Maheemal/Spacemouse-Macro-Keys/Source Files/PCB/Spacemouse-Macro-Keys.kicad_sch

## KiCad design Source Files/PCB/Spacemouse-Macro-Keys.kicad_sch (2022-12-31)

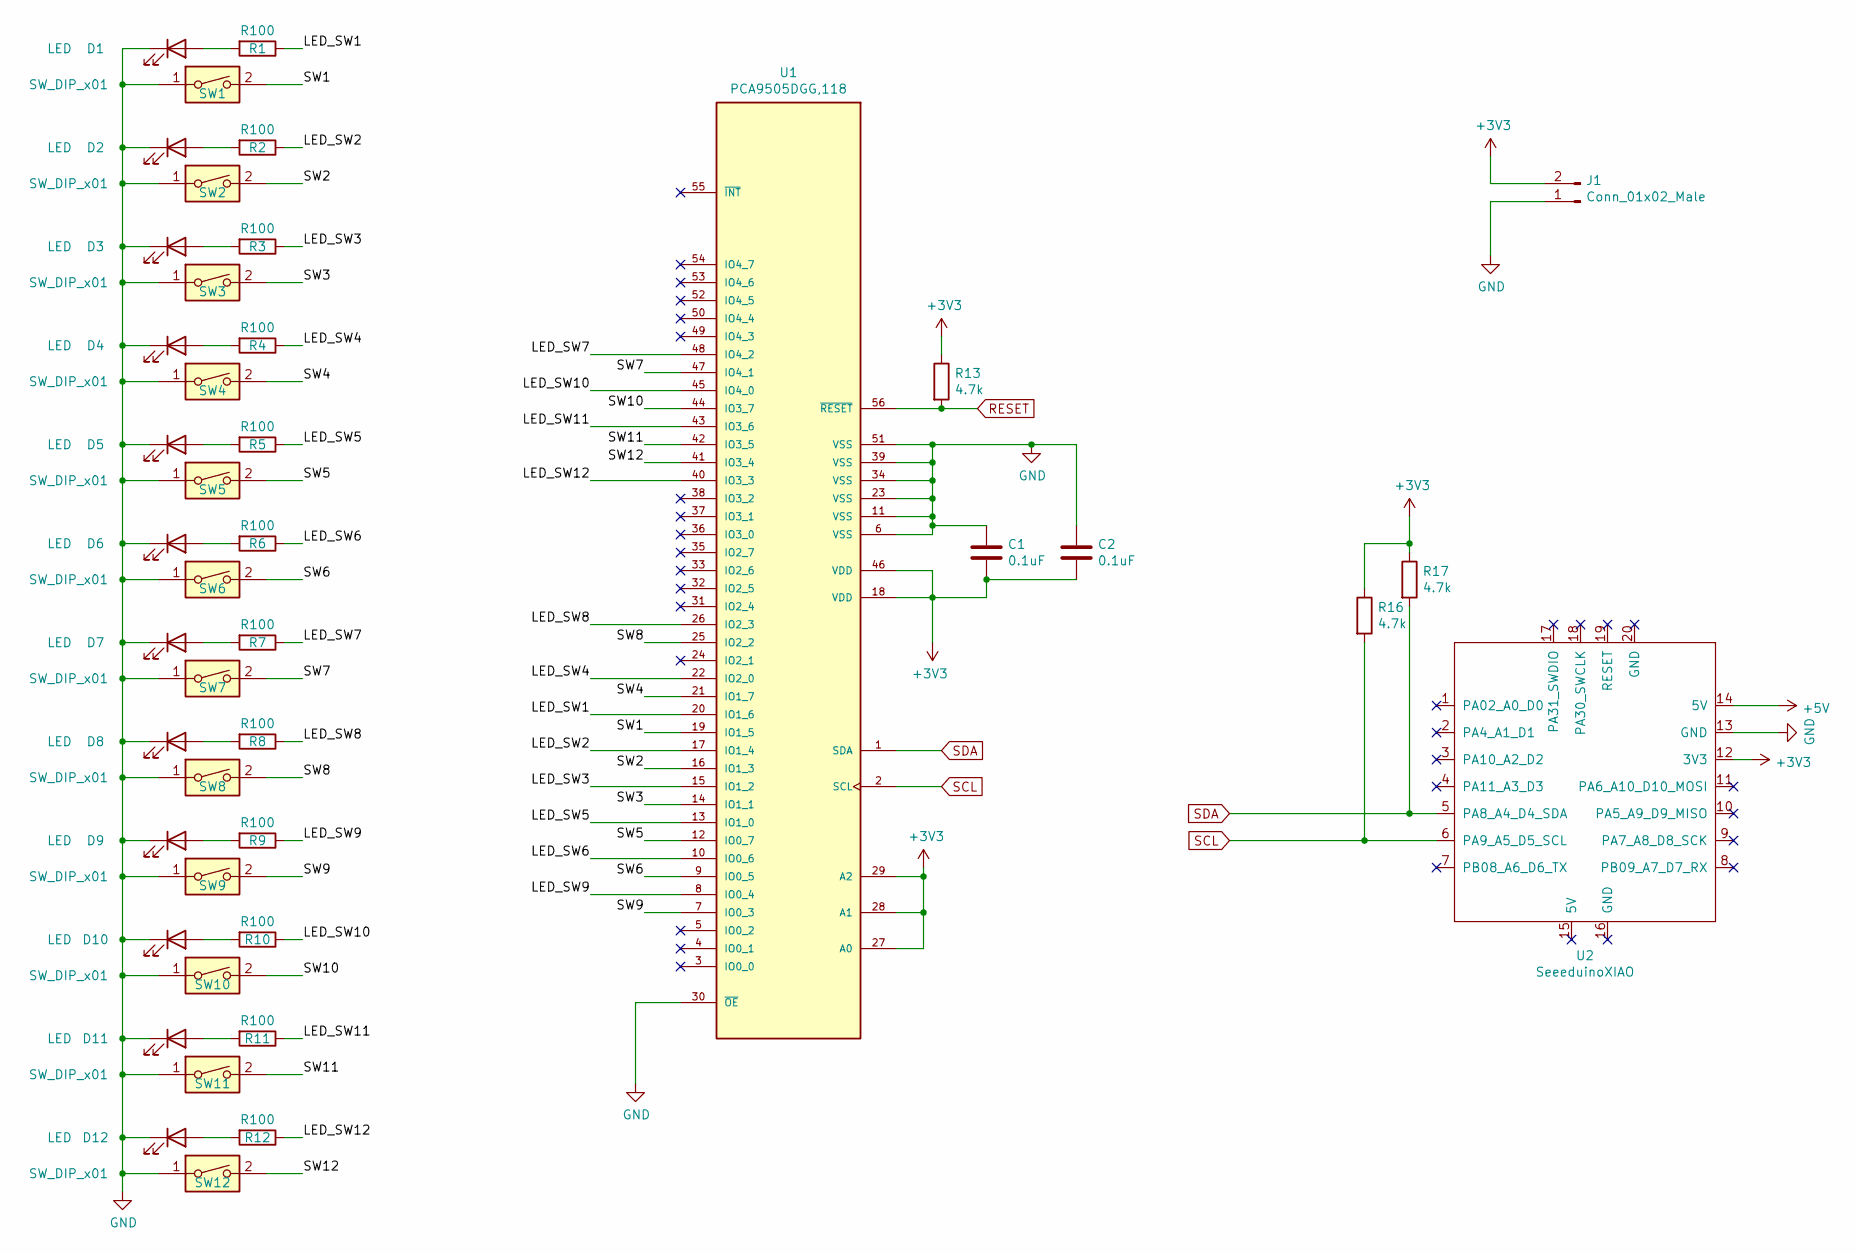
[picture p8: schematic Spacemouse-Macro-Keys.kicad_sch]

Parts:
C1, C2: 0.1uF; C_0603_1608Metric
D1, D2, D3, D4, D5, D6, D7, D8, D9, D10, D11, D12: LED; LED_0603_1608Metric
J1: Conn_01x02_Male; PinHeader_1x02_P2.54mm_Vertical
R1, R2, R3, R4, R5, R6, R7, R8, R9, R10, R11, R12: R100; R_0603_1608Metric
R13, R16, R17: 4.7k; R_0603_1608Metric
SW1, SW2, SW3, SW4, SW5, SW6, SW7, SW8, SW9, SW10, SW11, SW12: SW_DIP_x01; SW_Kailh_Choc_V1
U1: PCA9505DGG,118; SOP50P810X120-56N; PARTREV 4
U2: SeeeduinoXIAO; Seeeduino XIAO-MOUDLE14P-2.54-21X17.8MM

Connections:
+3V3: C1.2, C2.2, J1.2, R13.1, R16.1, R17.1, U1.18 (VDD), U1.27 (A0), U1.28 (A1), U1.29 (A2), U1.46 (VDD), U2.12 (3V3)
+5V: U2.14 (5V)
GND: C1.1, C2.1, D1.1 (K), D2.1 (K), D3.1 (K), D4.1 (K), D5.1 (K), D6.1 (K), D7.1 (K), D8.1 (K), D9.1 (K), D10.1 (K), D11.1 (K), D12.1 (K), J1.1, SW1.1, SW2.1, SW3.1, SW4.1, SW5.1, SW6.1, SW7.1, SW8.1, SW9.1, SW10.1, SW11.1, SW12.1, U1.6 (VSS), U1.11 (VSS), U1.23 (VSS), U1.30 (~OE), U1.34 (VSS), U1.39 (VSS), U1.51 (VSS), U2.13 (GND)
LED_SW1: R1.1, U1.20 (IO1_6)
LED_SW2: R2.1, U1.17 (IO1_4)
LED_SW3: R3.1, U1.15 (IO1_2)
LED_SW4: R4.1, U1.22 (IO2_0)
LED_SW5: R5.1, U1.13 (IO1_0)
LED_SW6: R6.1, U1.10 (IO0_6)
LED_SW7: R7.1, U1.48 (IO4_2)
LED_SW8: R8.1, U1.26 (IO2_3)
LED_SW9: R9.1, U1.8 (IO0_4)
LED_SW10: R10.1, U1.45 (IO4_0)
LED_SW11: R11.1, U1.43 (IO3_6)
LED_SW12: R12.1, U1.40 (IO3_3)
unnamed: D1.2 (A), R1.2
unnamed: D2.2 (A), R2.2
unnamed: D3.2 (A), R3.2
unnamed: D4.2 (A), R4.2
unnamed: D5.2 (A), R5.2
unnamed: D6.2 (A), R6.2
unnamed: D7.2 (A), R7.2
unnamed: D8.2 (A), R8.2
unnamed: D9.2 (A), R9.2
unnamed: D10.2 (A), R10.2
unnamed: D11.2 (A), R11.2
unnamed: D12.2 (A), R12.2
RESET: R13.2, U1.56 (~RESET)
SCL: R16.2, U1.2 (SCL), U2.6 (PA9_A5_D5_SCL)
SDA: R17.2, U1.1 (SDA), U2.5 (PA8_A4_D4_SDA)
SW1: SW1.2, U1.19 (IO1_5)
SW2: SW2.2, U1.16 (IO1_3)
SW3: SW3.2, U1.14 (IO1_1)
SW4: SW4.2, U1.21 (IO1_7)
SW5: SW5.2, U1.12 (IO0_7)
SW6: SW6.2, U1.9 (IO0_5)
SW7: SW7.2, U1.47 (IO4_1)
SW8: SW8.2, U1.25 (IO2_2)
SW9: SW9.2, U1.7 (IO0_3)
SW10: SW10.2, U1.44 (IO3_7)
SW11: SW11.2, U1.42 (IO3_5)
SW12: SW12.2, U1.41 (IO3_4)
